Dh-Van/eclectronics-mp1/ltspice/sim.asc

C1: cap; {mc(0.1u, 0.05)}
D1: LED
R1: res; {mc(4.99k, 0.01)}
R2: res; {mc(4.99k, 0.01)}
R3: res; {mc(40.2k, 0.01)}
R4: res; {mc(20k, 0.01)}
R5: res; {mc(3.01Meg, 0.01)}; tol=1
R6: res; {mc(110, 0.01)}
U1: UniversalOpAmp2
V1: voltage; 3.3
Named nets: 0, Vdd, Vth, vp, vn, out
.tran 0 6 0 1m
.step param run 1 500 1
.ic V(vn)=0
 
.meas TRAN t1 WHEN V(out)=1.65 RISE=2
.meas TRAN t2 WHEN V(out)=1.65 RISE=3
.meas TRAN period PARAM t2-t1
